mjeanrichard/BatLogger/circuit/LTSpice/UltrasonicAmp.asc

C1: polcap; 100µ; V=6.3 Irms=175m Rser=0.65 Lser=0 mfg="Panasonic" pn="ECA0JFQ101" type="Al electrolytic"
C2: polcap; 0.33µ
C3: polcap; 0.1µ
C4: polcap; 100µ
C5: cap; 0.1µ
C7: cap; 4.7n
C8: cap; 4.7n
C9: polcap; 0.1µ
MIC: voltage; SINE(0 0.01 500); AC 1m
POT2: res; 25k
POT: res; 25k
R1: res; 100
R2: res; 10k
R3: res; 470
R4: res; 1k
R5: res; 1k
R6: res; 5k
R7: res; 5k
R8: res; 100k
R9: res; 1k
R11: res; 4.7meg
R12: res; 1k
U1: opamp2; OPA134
U2: opamp2; OPA134
U3: opamp2; OPA134
U4: LM339
V1: voltage; 5
Named nets: 0, 5V, OUT
.tran 5m
.inc OPA134.sub
