mjeanrichard/BatLogger/circuit/LTSpice/UltrasonicPreamp4.asc

C1: cap; 1n
C2: cap; 100n
C3: cap; 1n
C4: cap; 100n
C8: cap; 100n
C9: cap; 1n
Mic: voltage; SINE(0 0.05m 3k); AC 1m
Q1: npn; 2N3904
Q2: npn; 2N3904
Q3: npn; 2N3904
Q4: npn; 2N3904
Q5: npn; 2N3904
R1: res; 10k
R2: res; 100k
R3: res; 18k
R4: res; 47k
R5: res; 4k7
R6: res; 47
R7: res; 10k
R8: res; 100k
R9: res; 18k
R10: res; 47k
R11: res; 4k7
R12: res; 47
R16: res; 100k
R17: res; 18k
R18: res; 10k
R19: res; 4k7
R20: res; 47k
R21: res; 47
U2: CD4024B
V2: voltage; 5
Named nets: 0, out, In, rect
.inc cd4000.lib
.tran .02 uic
Sim only
