mjeanrichard/BatLogger/circuit/LTSpice/UltrasonicPreampLm386.asc

C1: cap; 1n
C2: cap; 100n
C3: cap; 1n
C4: cap; 100n
C5: cap; 10µ
C6: cap; 0.05µ
C7: cap; 1n
Mic: voltage; SINE(0 0.05m 5k); AC 1m
Q1: npn; 2N3904
Q2: npn; 2N3904
Q3: npn; 2N3904
R1: res; 10k
R2: res; 100k
R3: res; 18k
R4: res; 47k
R5: res; 4k7
R6: res; 47
R7: res; 10k
R8: res; 100k
R9: res; 18k
R10: res; 47k
R11: res; 4k7
R12: res; 47
R13: res; 0
R14: res; 10
R15: res; 18k
U1: lm386
U2: CD4024B
V2: voltage; 5
Named nets: 0, out, In, rect
.inc cd4000.lib
.tran .02 uic
Sim only
